rritterson/computeblade-adapter/pcb/compute-blade-dda-adapter.kicad_sch

## KiCad design pcb/compute-blade-dda-adapter.kicad_sch (2026-09-22)

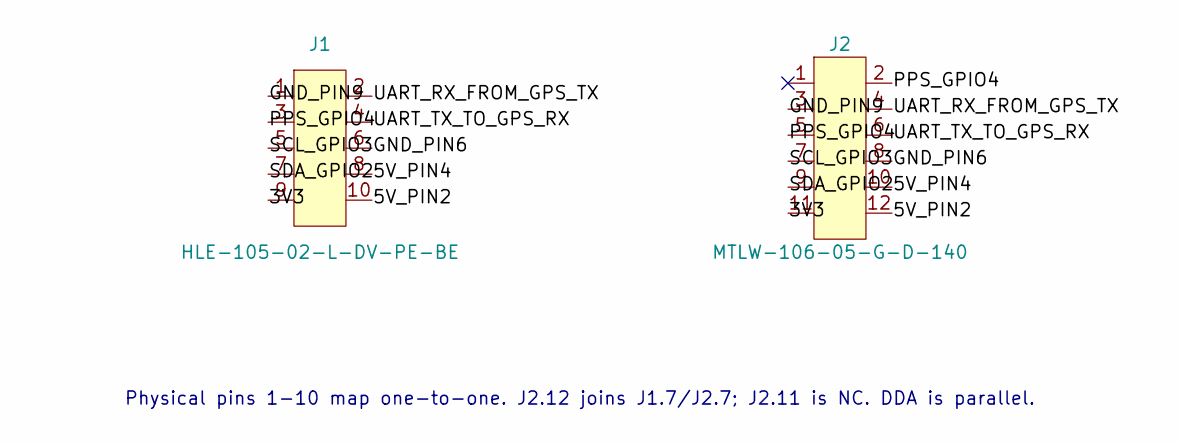
[picture p5: schematic compute-blade-dda-adapter.kicad_sch]

Parts:
J1: HLE-105-02-L-DV-PE-BE; Samtec_HLE-105-02-L-DV-PE-BE
J2: MTLW-106-05-G-D-140; Samtec_MTLW-106-05-G-D-140

Connections:
3V3: J1.9, J2.11
5V_PIN2: J1.10, J2.12
5V_PIN4: J1.8, J2.10
GND_PIN6: J1.6, J2.8
GND_PIN9: J1.1, J2.3
PPS_GPIO4: J1.3, J2.2, J2.5
SCL_GPIO3: J1.5, J2.7
SDA_GPIO2: J1.7, J2.9
UART_RX_FROM_GPS_TX: J1.2, J2.4
UART_TX_TO_GPS_RX: J1.4, J2.6

Notes on the sheet:
Physical pins 1-10 map one-to-one. J2.12 joins J1.7/J2.7; J2.11 is NC. DDA is parallel.
